boert/16M2164-Ersatz/Variante_R/1984_09__ct__8-Bit-Refresh_fuer_Z80.jpg

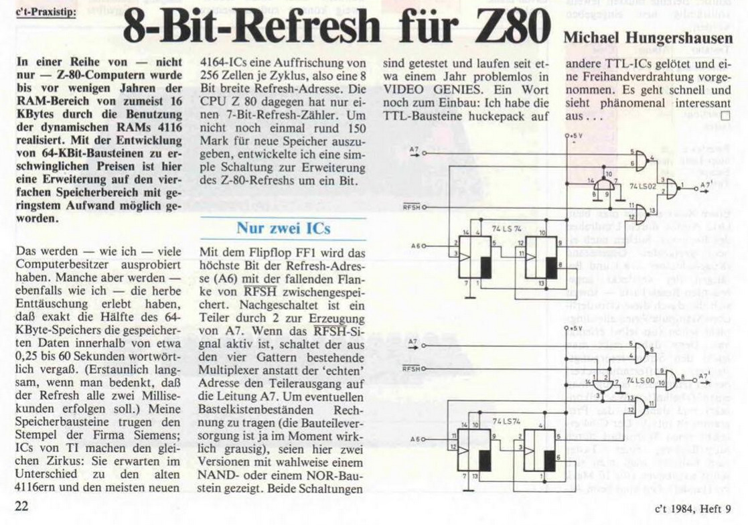
Variante_R/1984_09__ct__8-Bit-Refresh_fuer_Z80.jpg
