boert/16M2164-Ersatz/Refresh-Test/Bilder/0070.jpg

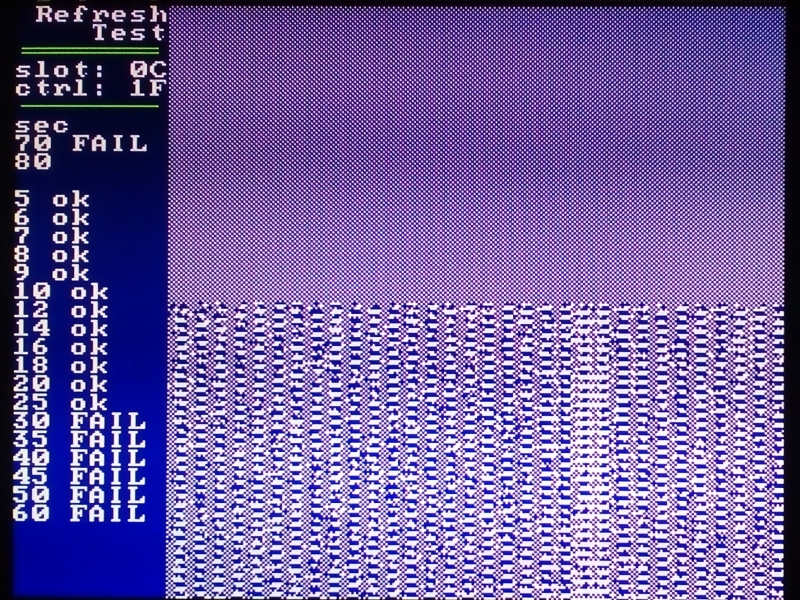
Refresh-Test/Bilder/0070.jpg
