boert/16M2164-Ersatz/Refresh-Test/Bilder/0090.jpg

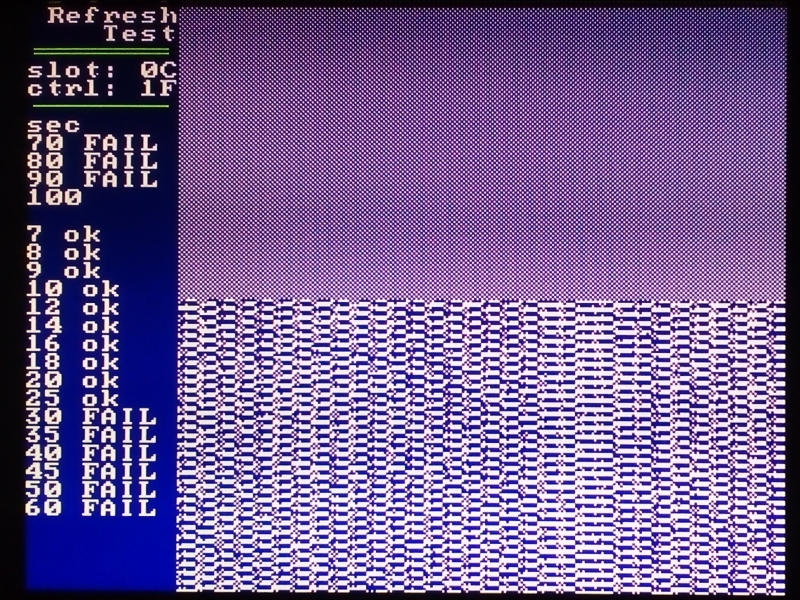
Refresh-Test/Bilder/0090.jpg
