boert/16M2164-Ersatz/Refresh-Test/Bilder/0100.jpg

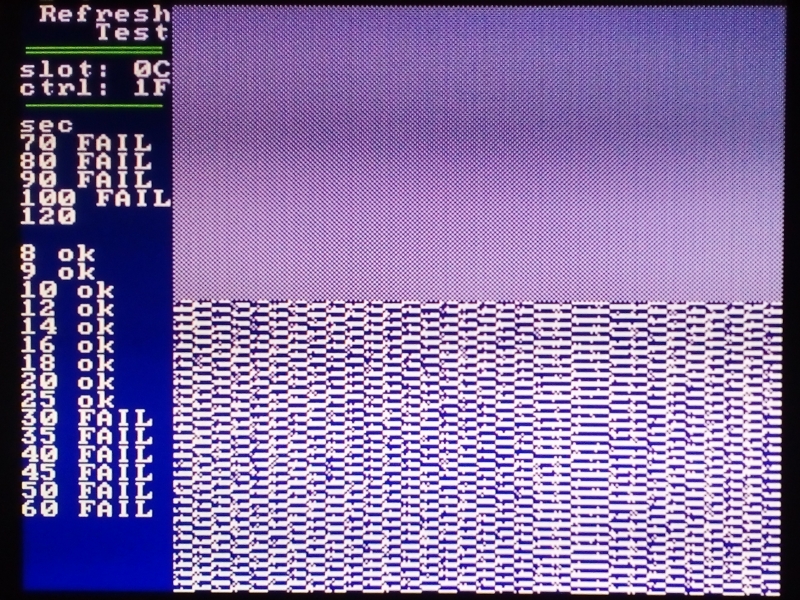
Refresh-Test/Bilder/0100.jpg
